chinawrj/FarmMesh-Node/hardware/rev-a/review/gerber/B_Cu.png

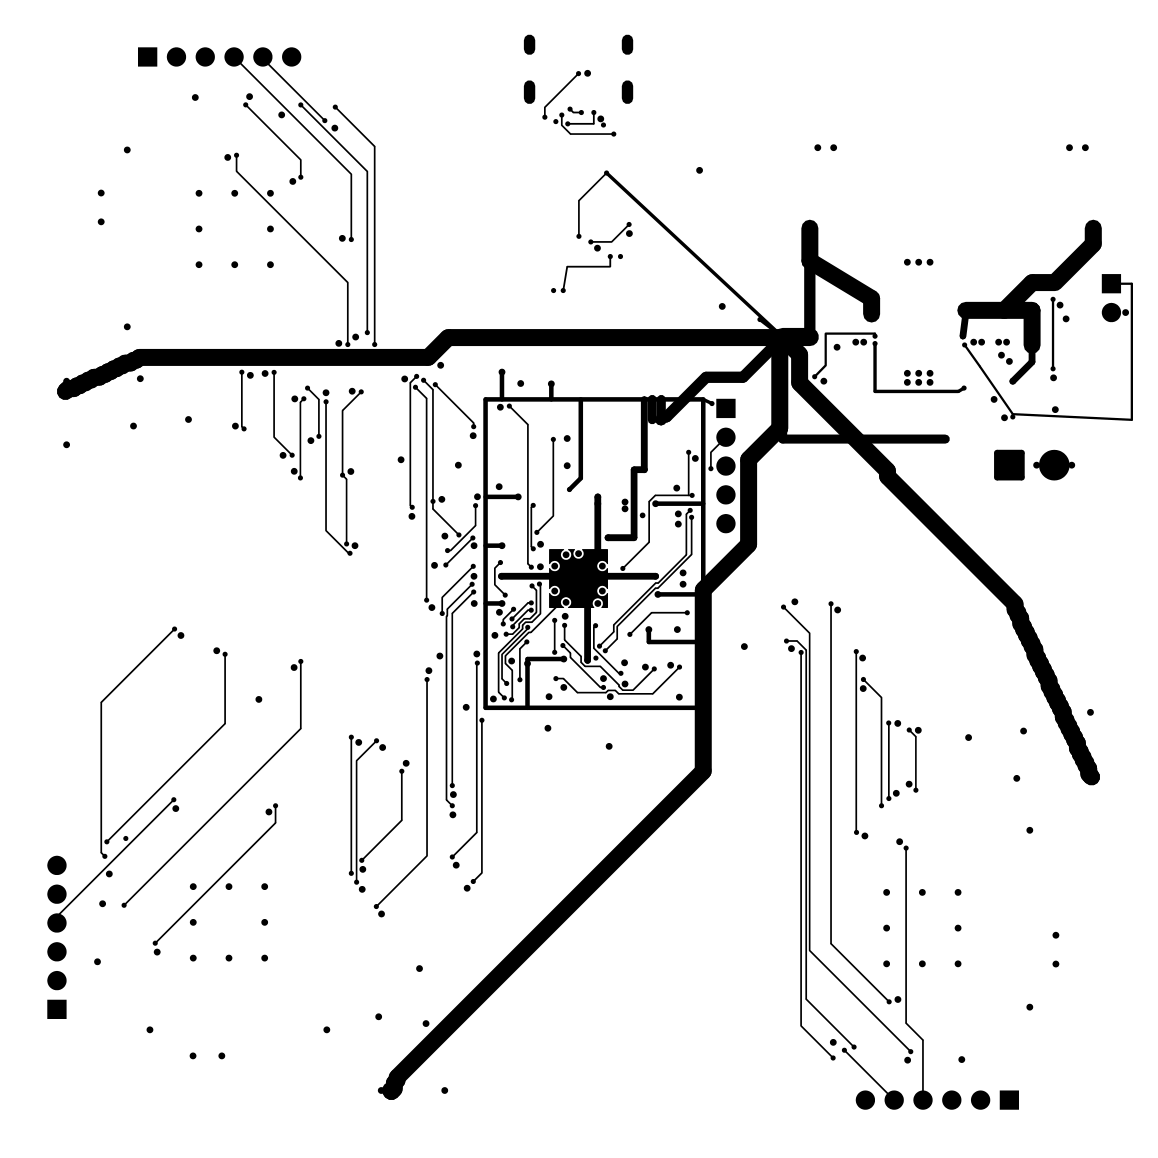
hardware/rev-a/review/gerber/B_Cu.png
