chinawrj/FarmMesh-Node/hardware/rev-a/review/gerber/In1_Cu.png

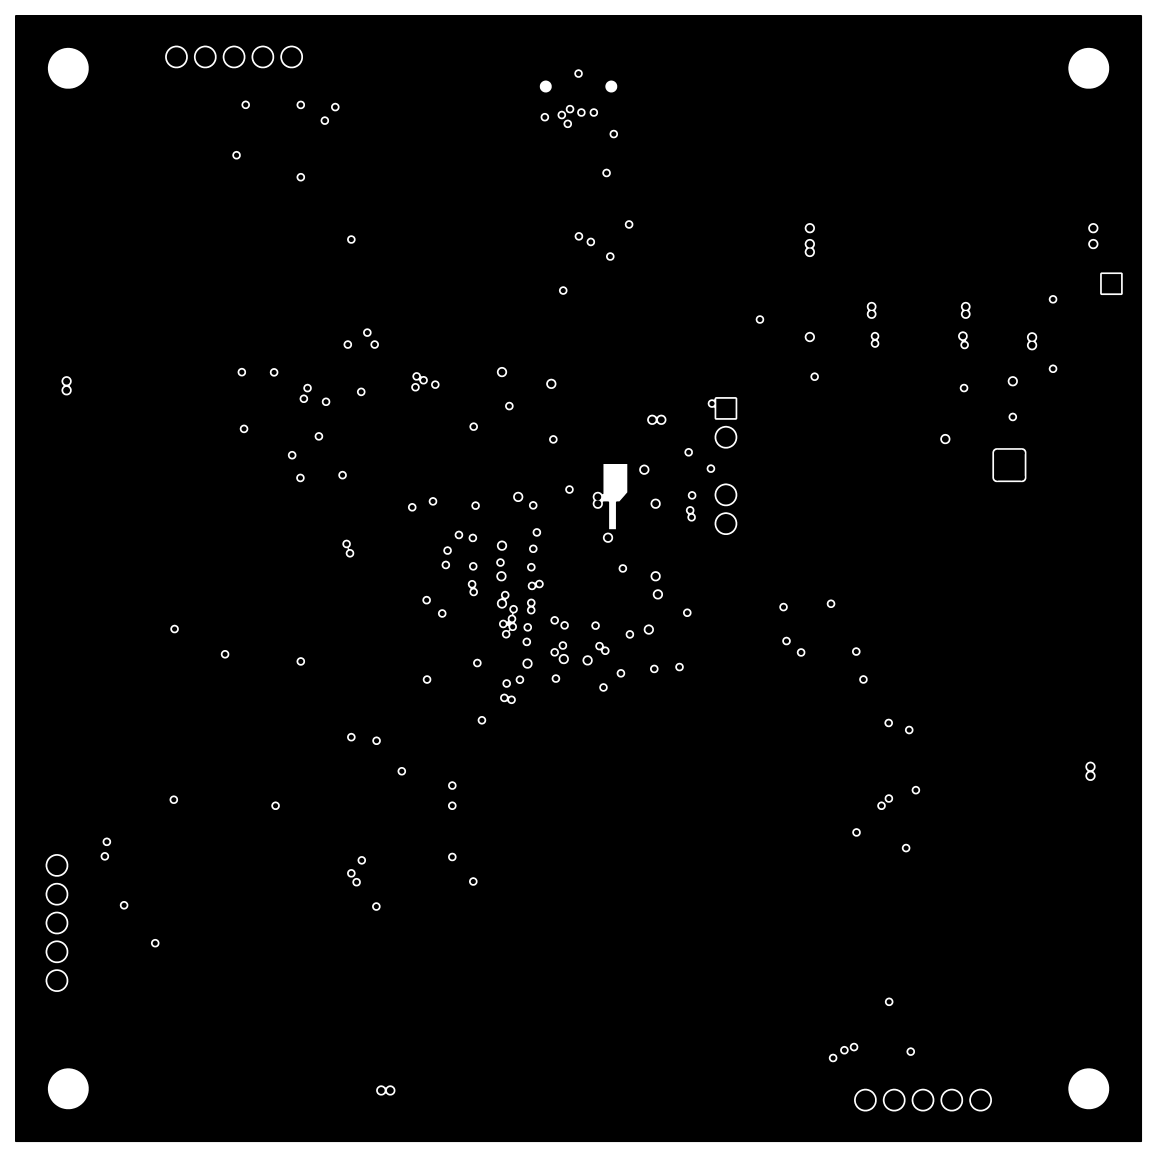
hardware/rev-a/review/gerber/In1_Cu.png
